frandallfarmer/3DProject/media/thumbnails/log-pillar-walls-2.jpg

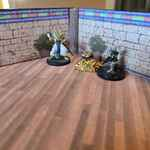
media/thumbnails/log-pillar-walls-2.jpg
