frandallfarmer/3DProject/media/thumbnails/log-wash-agregate-brush.jpg

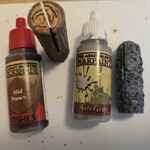
media/thumbnails/log-wash-agregate-brush.jpg
