frandallfarmer/3DProject/wall-templates/1 inch wall template.png

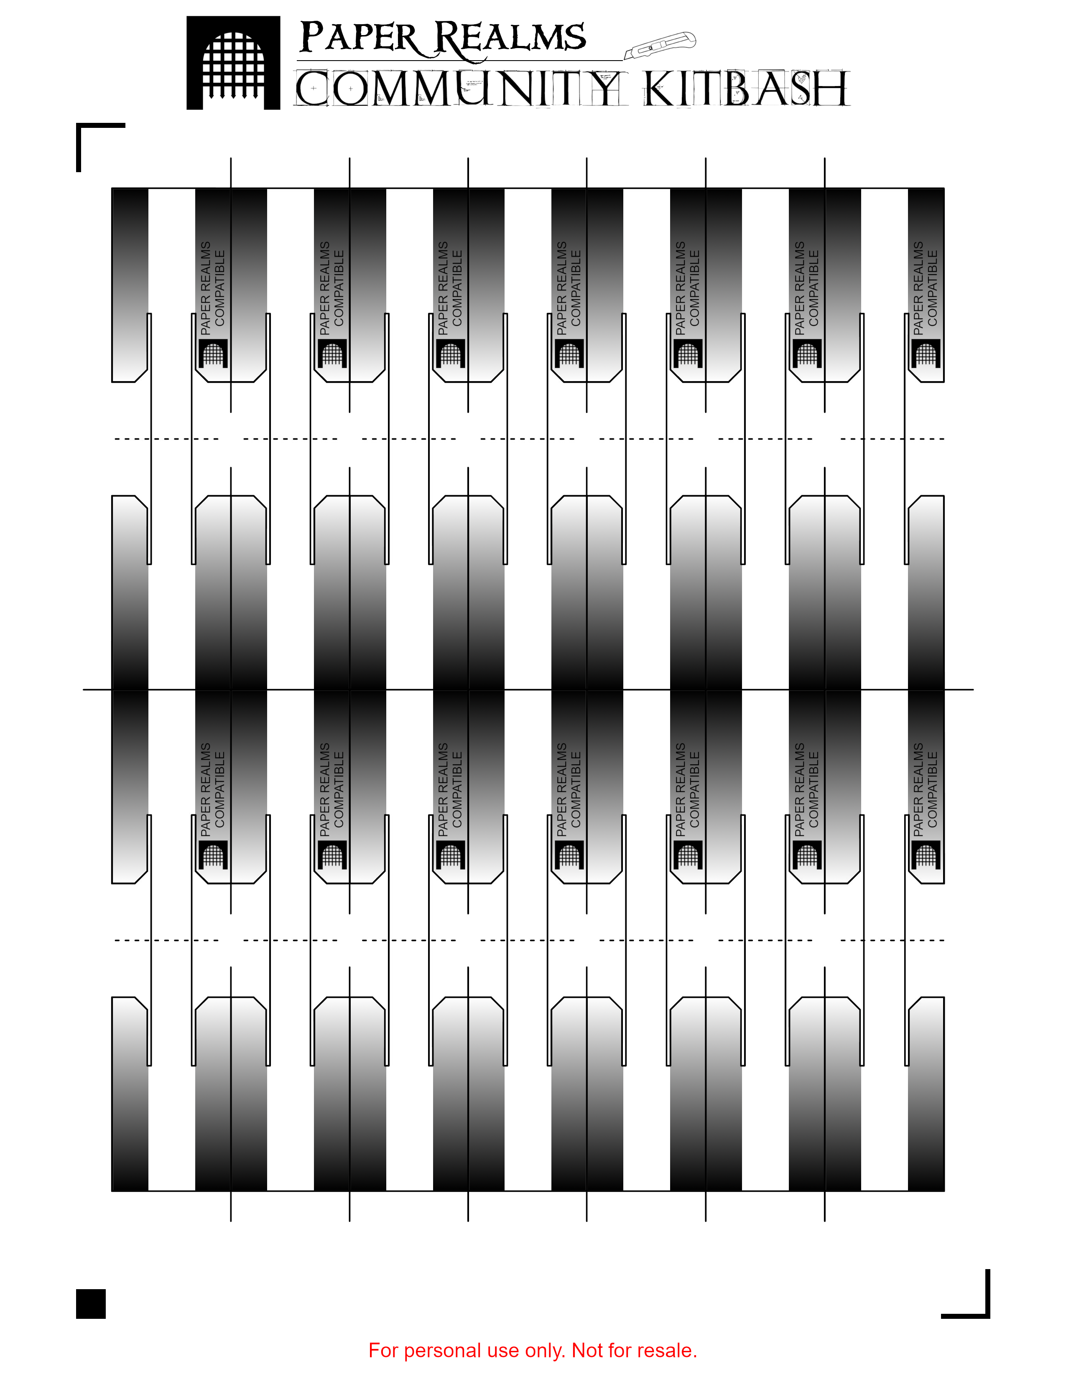
wall-templates/1 inch wall template.png
