frandallfarmer/3DProject/wall-templates/2 inch wall template.png

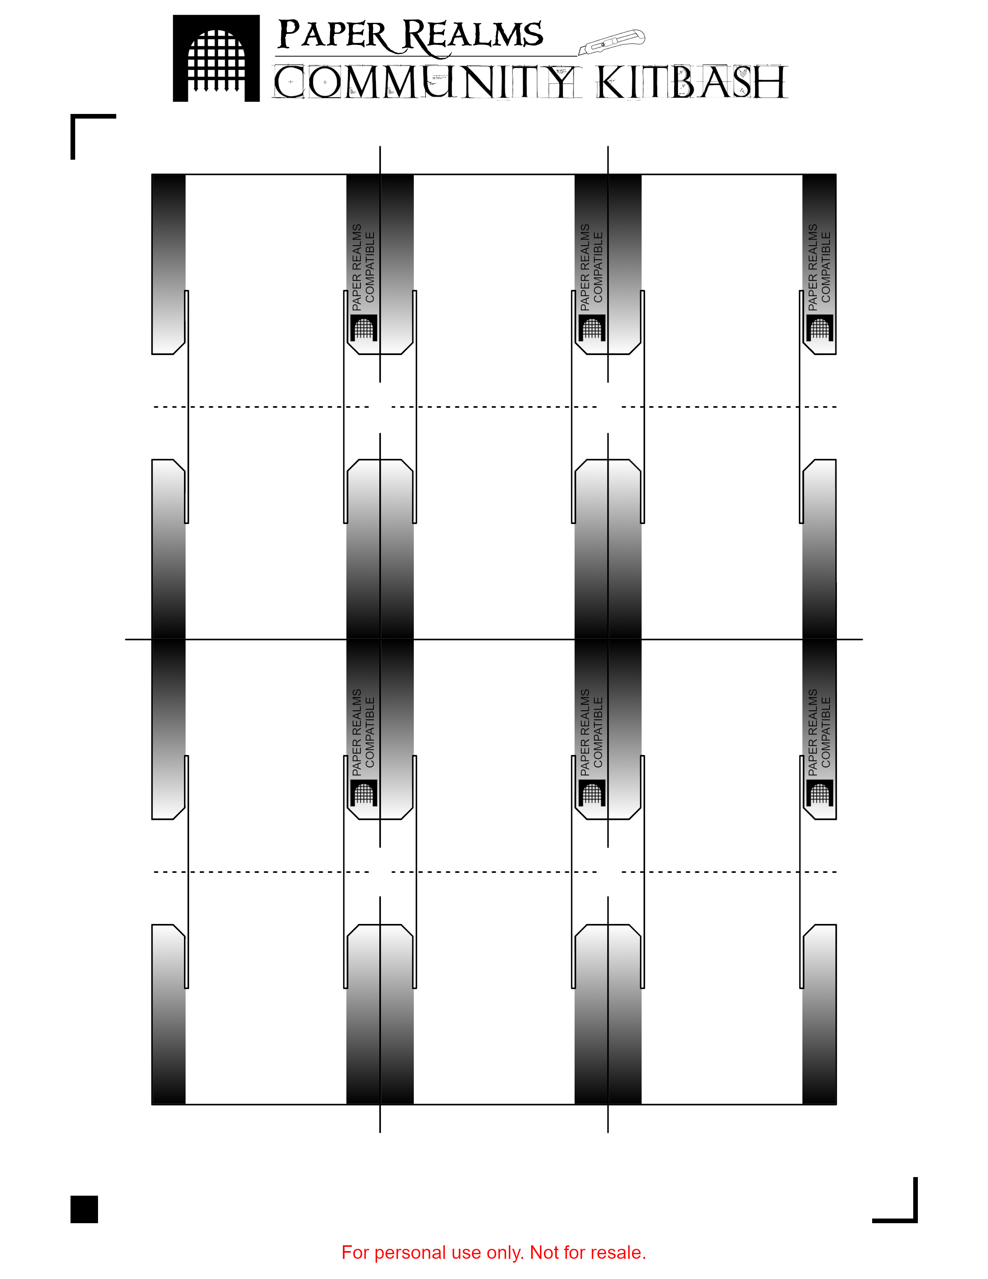
wall-templates/2 inch wall template.png
