frandallfarmer/3DProject/wall-templates/3 inch wall template.png

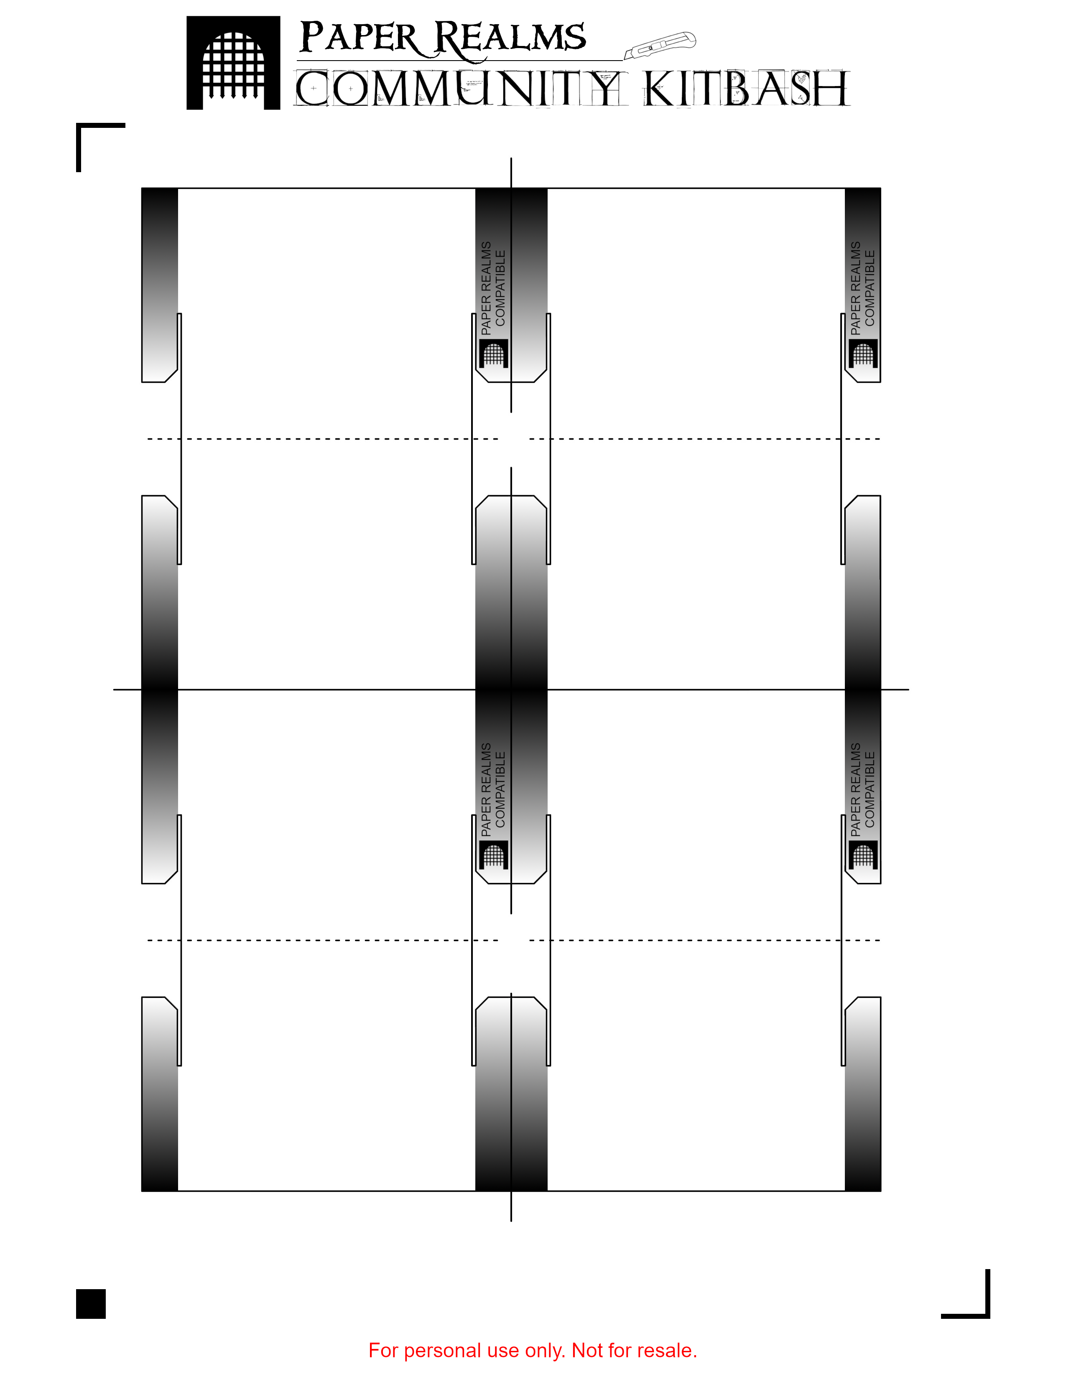
wall-templates/3 inch wall template.png
