frandallfarmer/3DProject/wall-templates/6 inch wall template.png

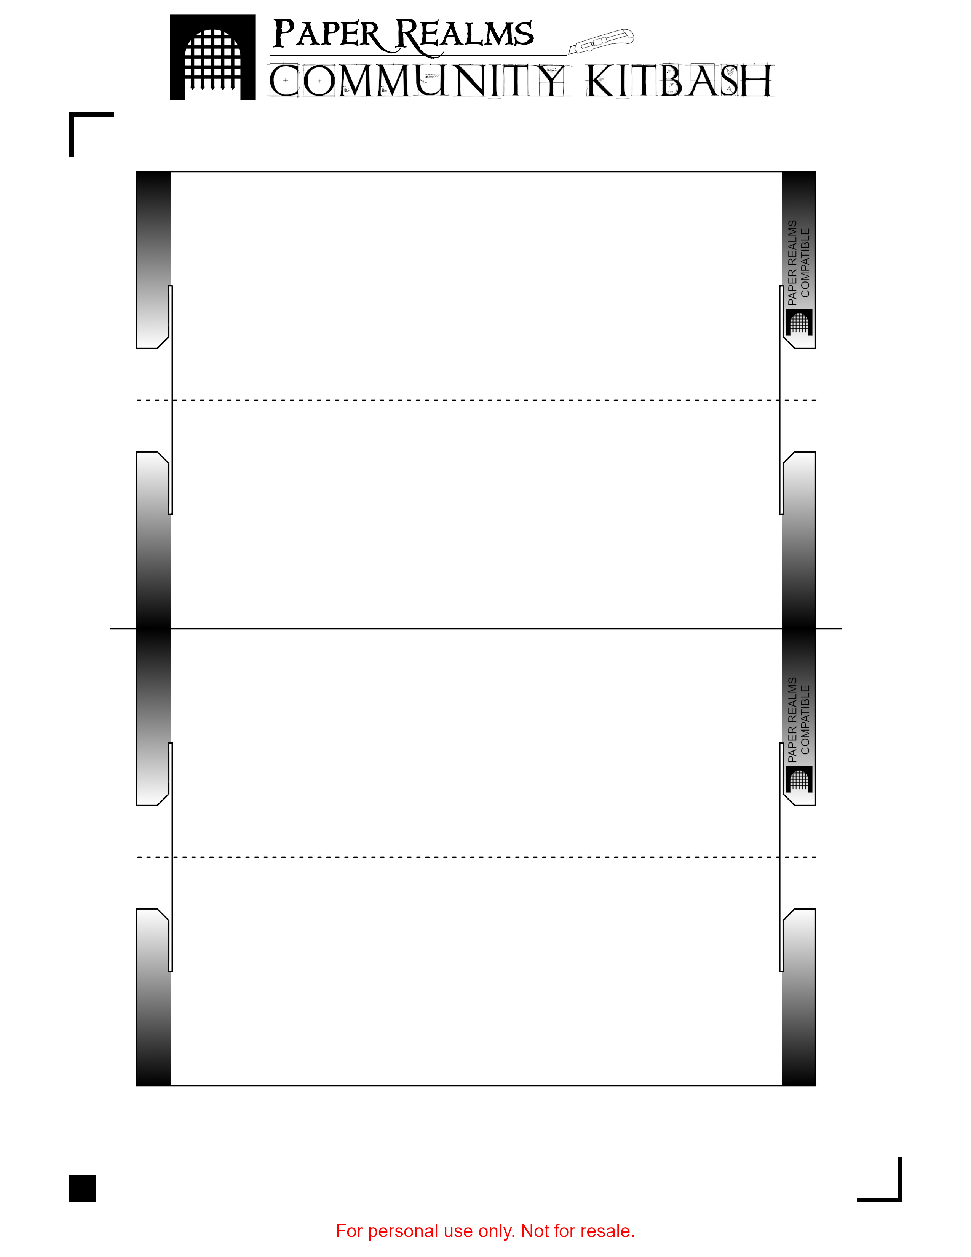
wall-templates/6 inch wall template.png
