frandallfarmer/3DProject/built_stls/output_cobblewall_straight.stl

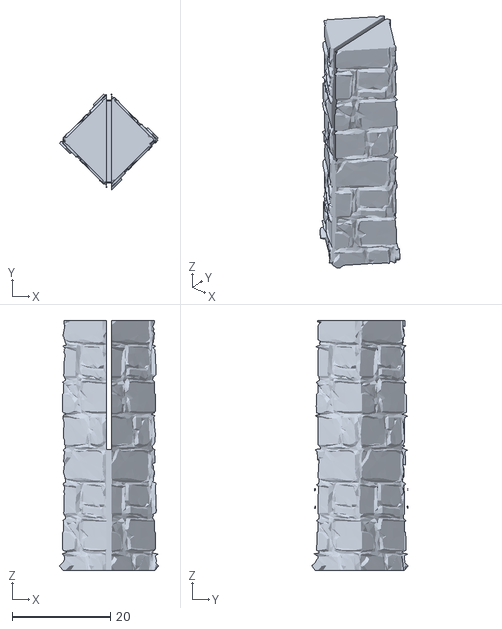
[picture p32: CAD file, 2025-12-31]
built_stls/output_cobblewall_straight.stl
20.1 x 19.5 x 50.8
