frandallfarmer/3DProject/src/pillar_cobblewall.stl

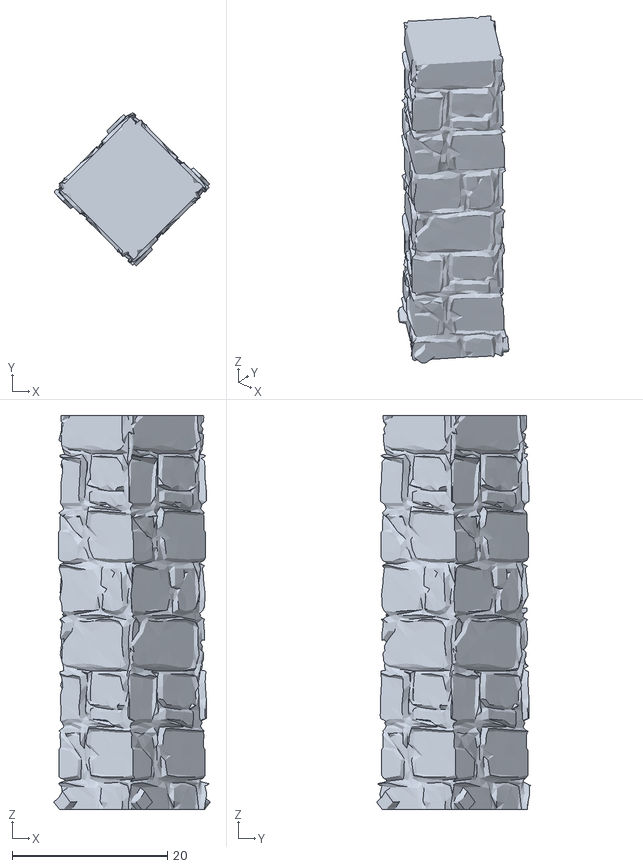
[picture p33: CAD file, 2025-12-16]
src/pillar_cobblewall.stl
20.1 x 19.7 x 50.8
