frandallfarmer/3DProject/src/pillar_cave.stl

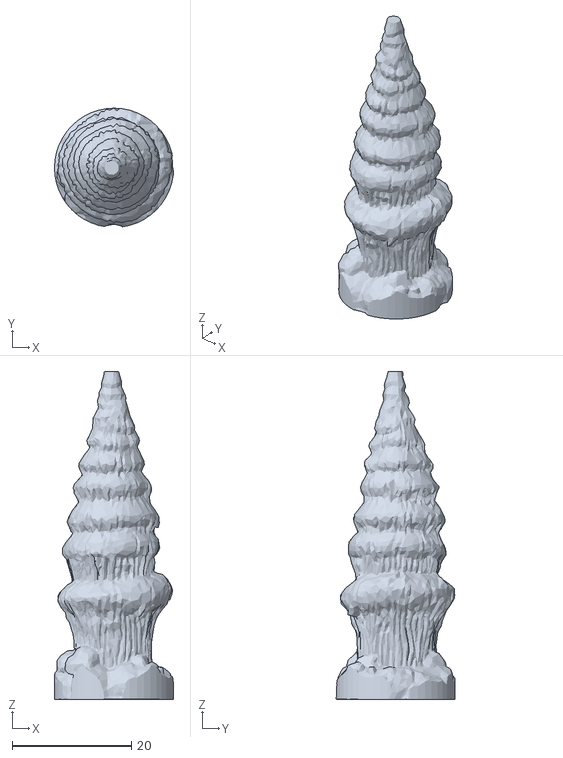
[picture p35: CAD file, 2025-12-16]
src/pillar_cave.stl
20.0 x 19.9 x 55.0
