frandallfarmer/3DProject/built_stls/output_hengestone_tee.stl

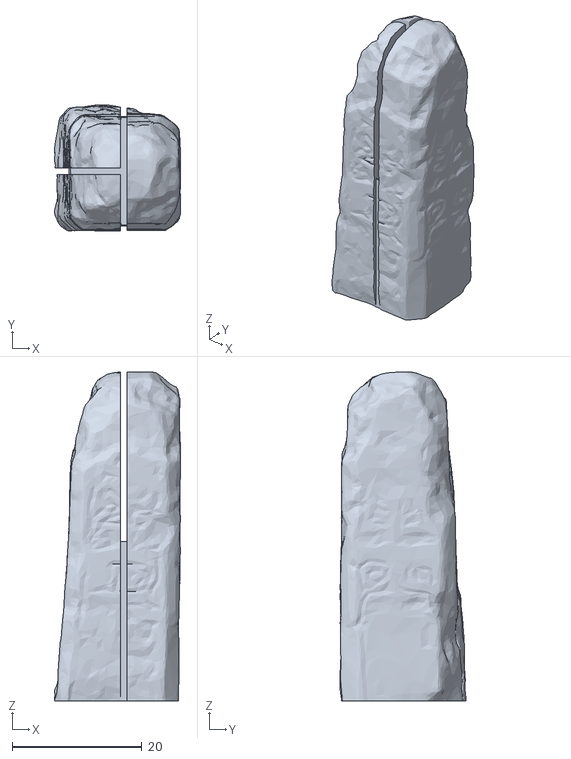
[picture p37: CAD file, 2025-12-31]
built_stls/output_hengestone_tee.stl
19.5 x 19.5 x 50.8
