frandallfarmer/3DProject/built_stls/output_cruciform_allways.stl

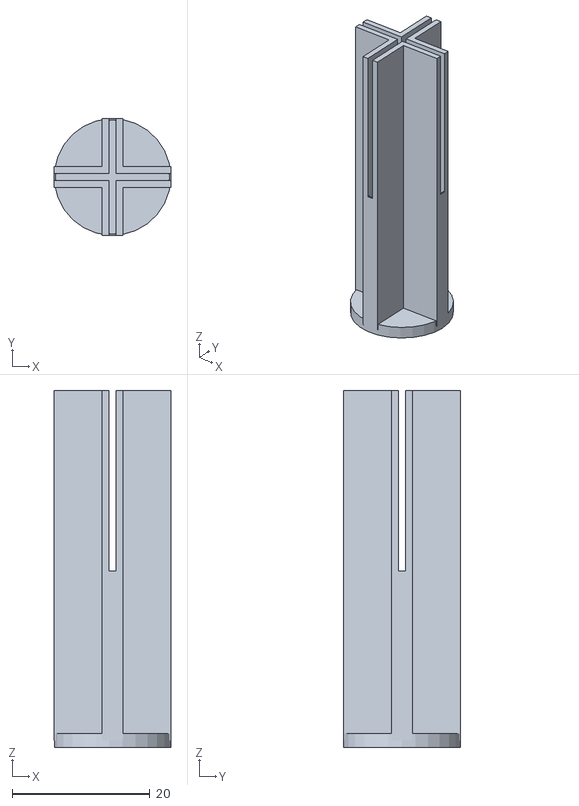
[picture p38: CAD file, 2025-12-31]
built_stls/output_cruciform_allways.stl
16.9 x 16.9 x 51.8
