frandallfarmer/3DProject/built_stls/output_cobblewall_allways.stl

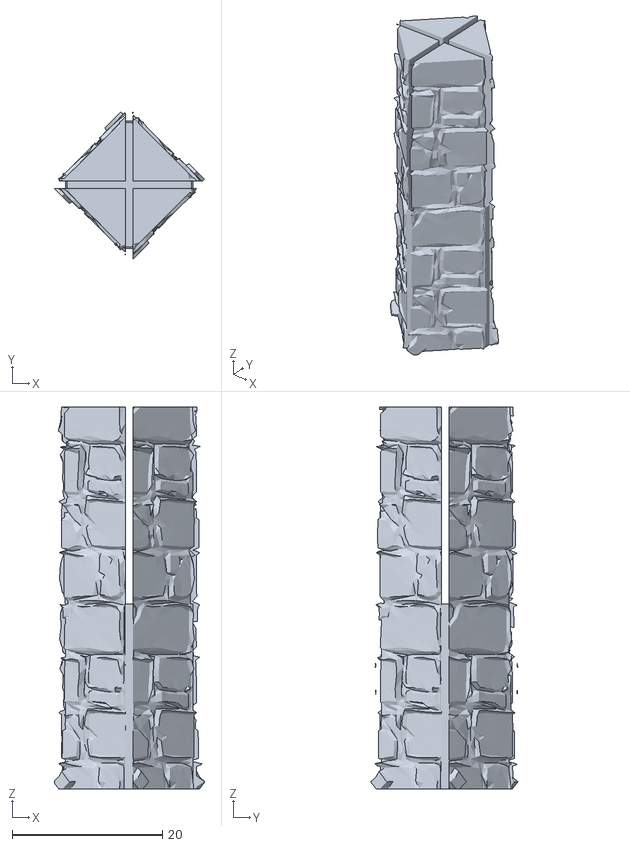
[picture p40: CAD file, 2025-12-31]
built_stls/output_cobblewall_allways.stl
20.0 x 19.5 x 50.8
