frandallfarmer/3DProject/built_stls/output_cruciform_tee.stl

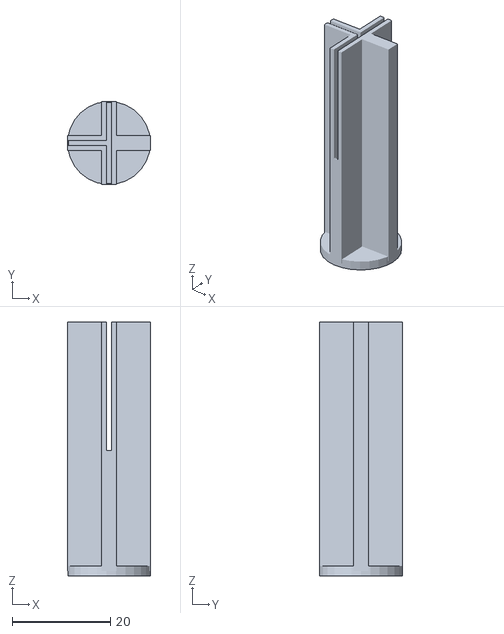
[picture p42: CAD file, 2025-12-31]
built_stls/output_cruciform_tee.stl
16.9 x 16.9 x 51.8
