frandallfarmer/3DProject/built_stls/output_origrect_end.stl

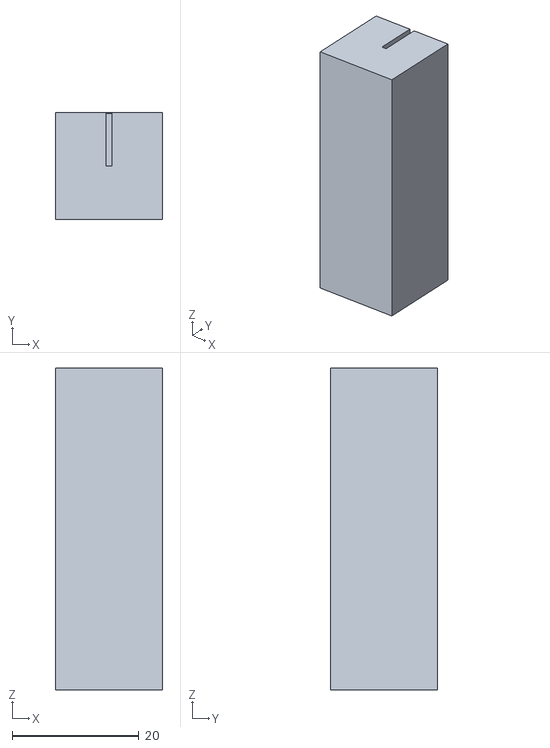
[picture p44: CAD file, 2025-12-31]
built_stls/output_origrect_end.stl
16.9 x 16.9 x 50.8
