frandallfarmer/3DProject/built_stls/output_slimrect_straight.stl

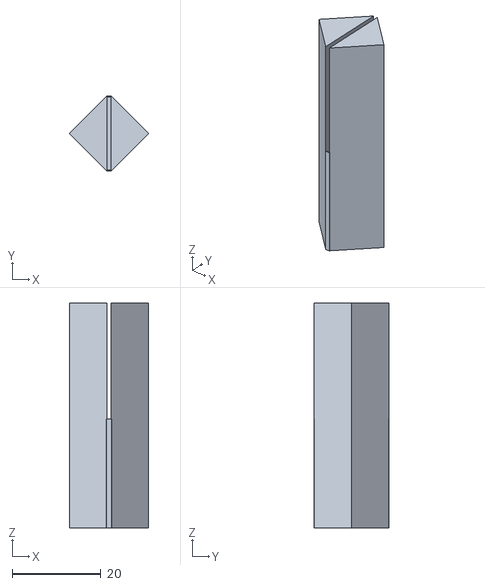
[picture p46: CAD file, 2025-12-31]
built_stls/output_slimrect_straight.stl
17.9 x 16.9 x 50.8
