frandallfarmer/3DProject/built_stls/output_origrect_tee.stl

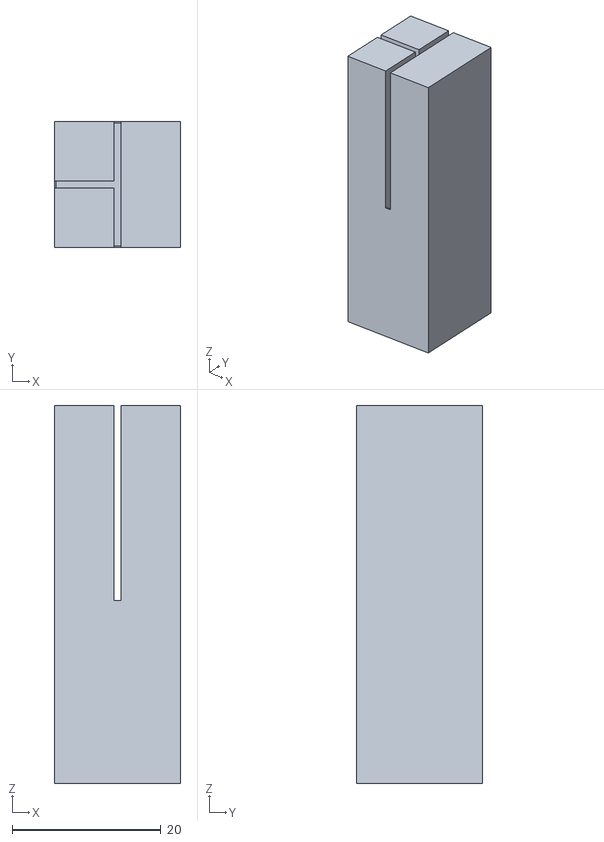
[picture p47: CAD file, 2025-12-31]
built_stls/output_origrect_tee.stl
16.9 x 16.9 x 50.8
