frandallfarmer/3DProject/built_stls/output_woodbeam_tee.stl

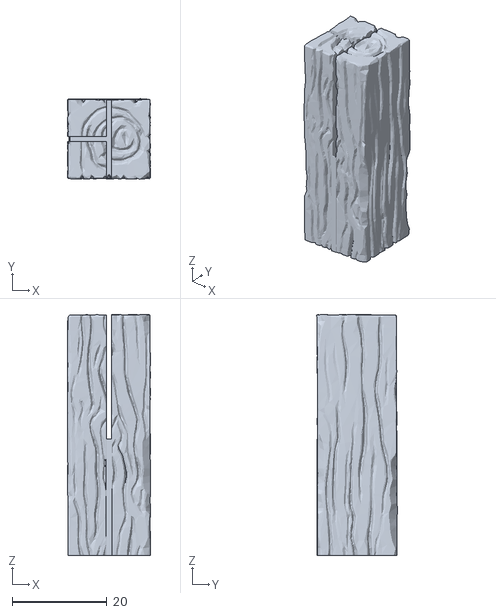
[picture p48: CAD file, 2025-12-31]
built_stls/output_woodbeam_tee.stl
17.5 x 17.0 x 50.8
