frandallfarmer/3DProject/built_stls/output_cobblewall_end.stl

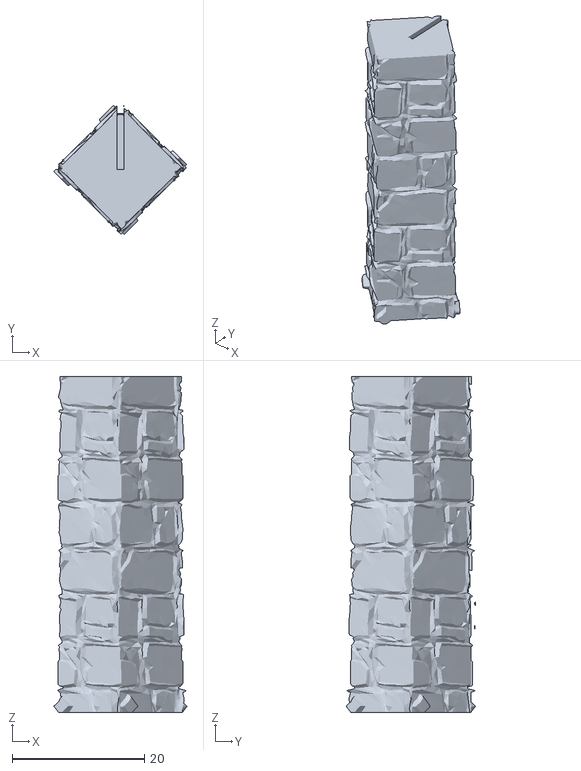
[picture p50: CAD file, 2025-12-31]
built_stls/output_cobblewall_end.stl
20.1 x 19.5 x 50.8
