frandallfarmer/3DProject/built_stls/output_stalagmite_allways.stl

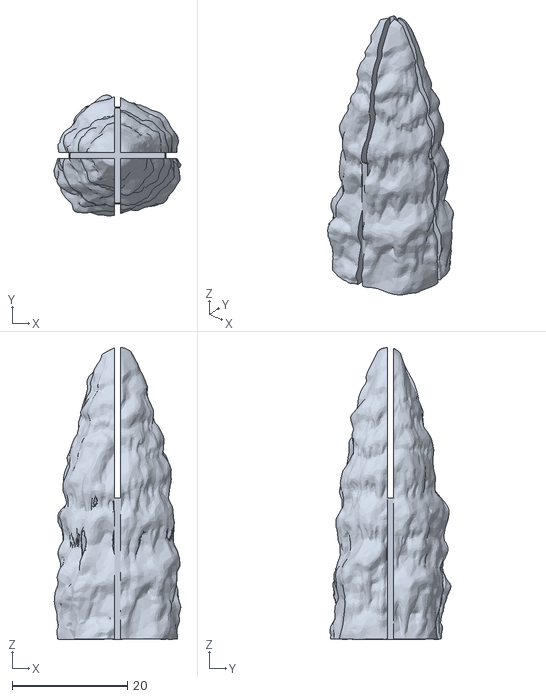
[picture p51: CAD file, 2025-12-31]
built_stls/output_stalagmite_allways.stl
22.0 x 21.0 x 50.7
