frandallfarmer/3DProject/built_stls/output_slimbeam_corner.stl

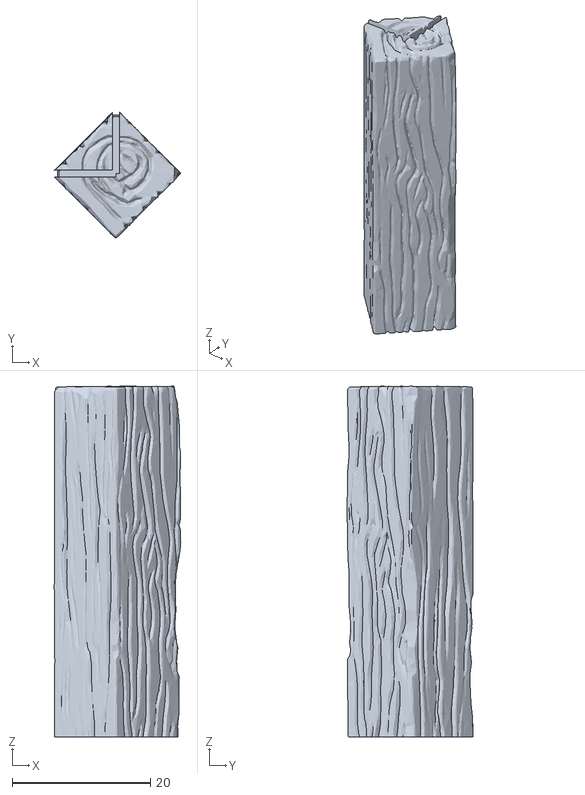
[picture p58: CAD file, 2025-12-31]
built_stls/output_slimbeam_corner.stl
18.3 x 18.2 x 50.8
