frandallfarmer/3DProject/built_stls/output_slimbeam_straight.stl

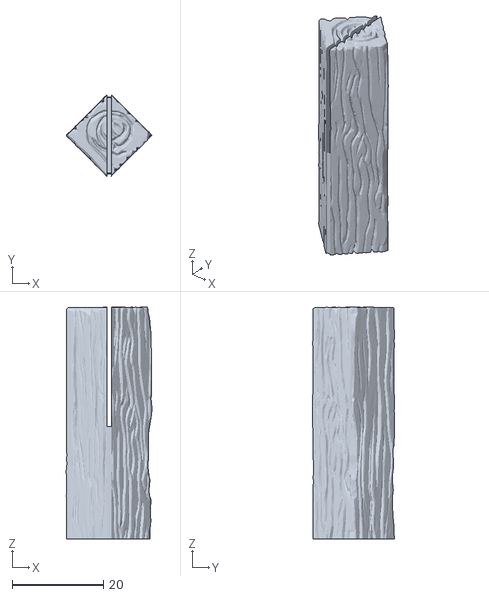
[picture p59: CAD file, 2025-12-31]
built_stls/output_slimbeam_straight.stl
18.8 x 17.9 x 50.8
