frandallfarmer/3DProject/built_stls/output_log_tee.stl

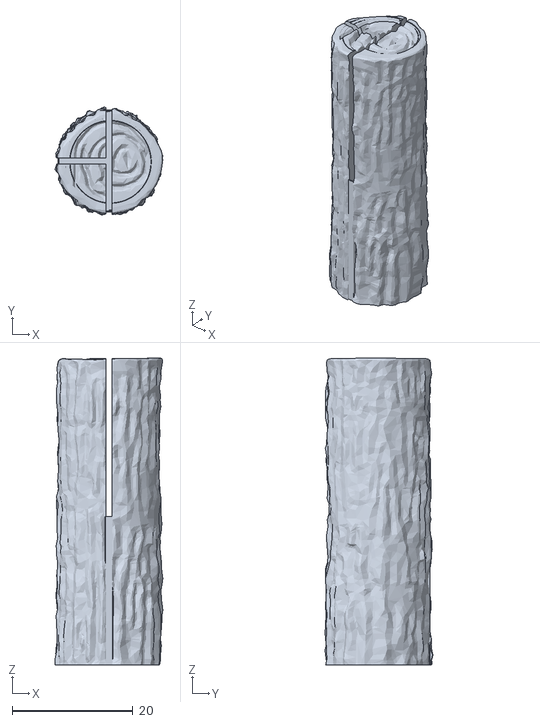
[picture p60: CAD file, 2025-12-31]
built_stls/output_log_tee.stl
17.8 x 17.9 x 50.8
