frandallfarmer/3DProject/built_stls/output_origrect_allways.stl

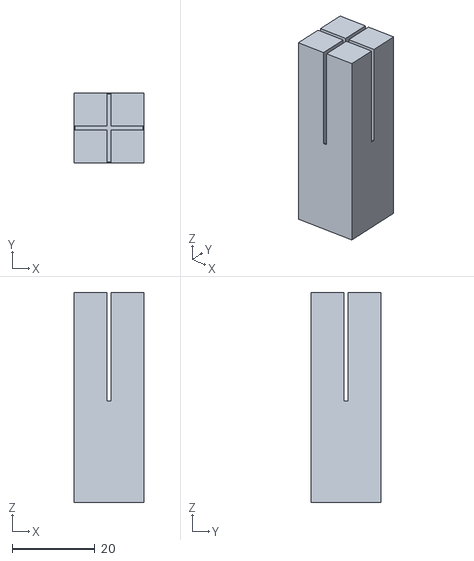
[picture p62: CAD file, 2025-12-31]
built_stls/output_origrect_allways.stl
16.9 x 16.9 x 50.8
