frandallfarmer/3DProject/built_stls/output_stalagmite_end.stl

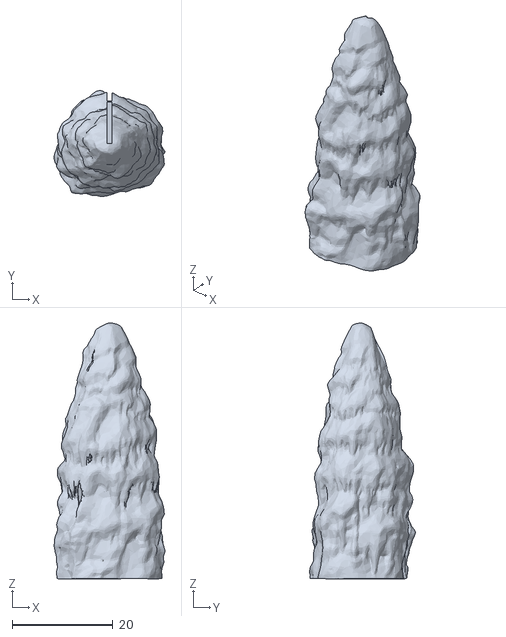
[picture p63: CAD file, 2025-12-31]
built_stls/output_stalagmite_end.stl
22.0 x 21.0 x 50.8
