frandallfarmer/3DProject/built_stls/output_cruciform_end.stl

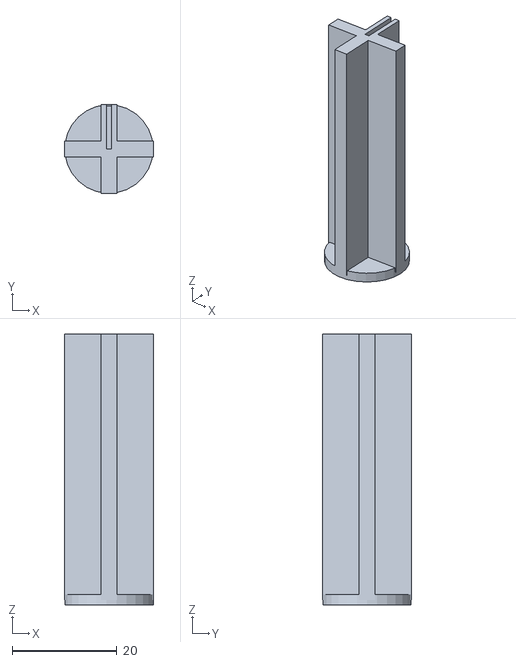
[picture p64: CAD file, 2025-12-31]
built_stls/output_cruciform_end.stl
16.9 x 16.9 x 51.8
