frandallfarmer/3DProject/built_stls/output_slimbeam_tee.stl

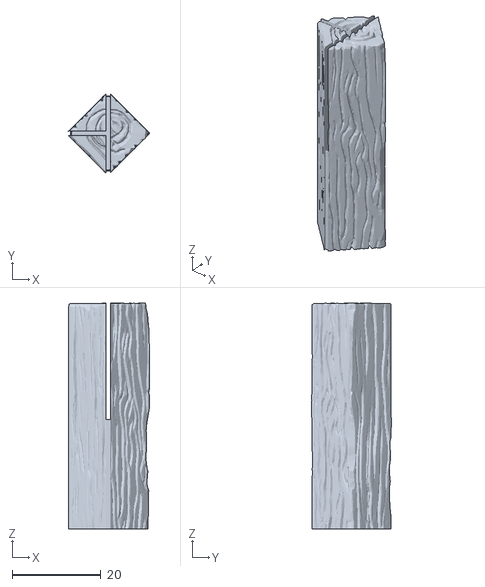
[picture p65: CAD file, 2025-12-31]
built_stls/output_slimbeam_tee.stl
18.3 x 17.9 x 50.8
