frandallfarmer/3DProject/built_stls/output_aggregate_end.stl

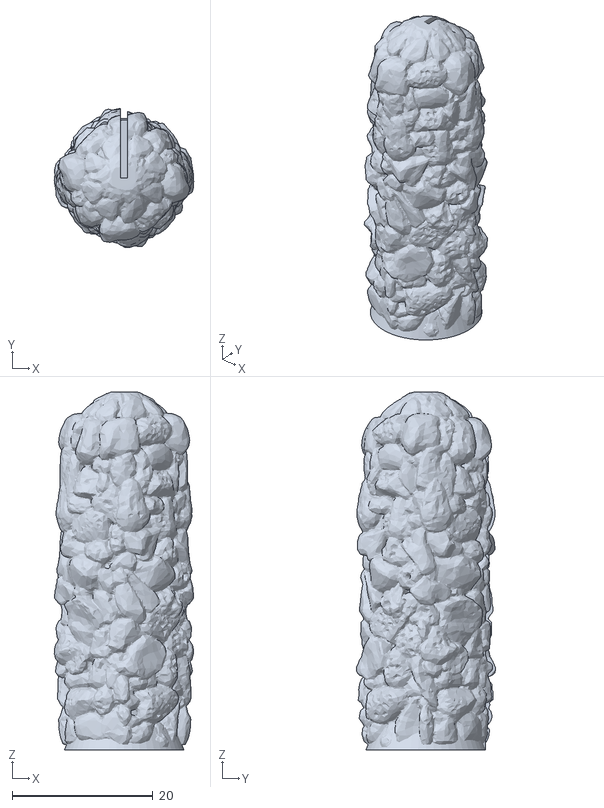
[picture p67: CAD file, 2025-12-31]
built_stls/output_aggregate_end.stl
19.8 x 19.8 x 50.8
