frandallfarmer/3DProject/built_stls/output_slimhengestone_allways.stl

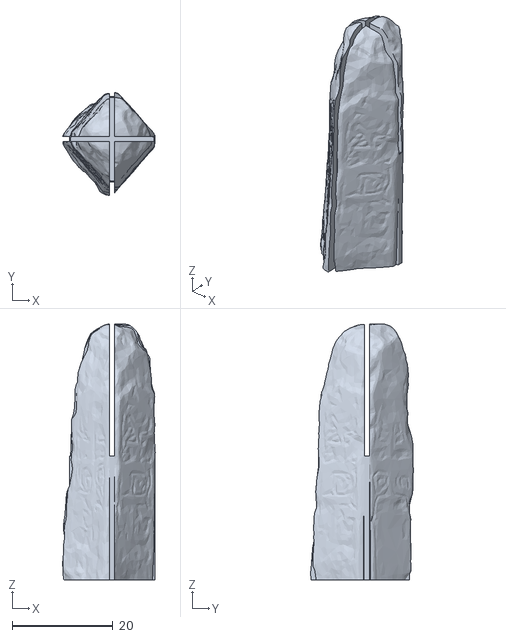
[picture p68: CAD file, 2025-12-31]
built_stls/output_slimhengestone_allways.stl
18.4 x 20.4 x 50.8
