frandallfarmer/3DProject/built_stls/output_woodbeam_allways.stl

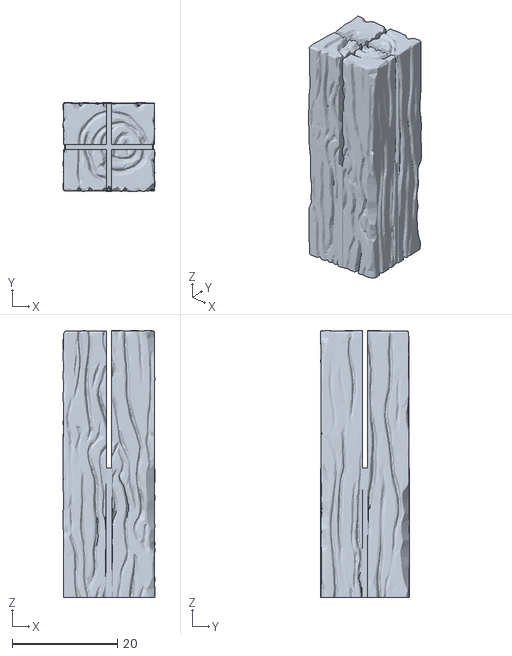
[picture p69: CAD file, 2025-12-31]
built_stls/output_woodbeam_allways.stl
17.5 x 17.0 x 50.8
