frandallfarmer/3DProject/built_stls/output_slimrect_corner.stl

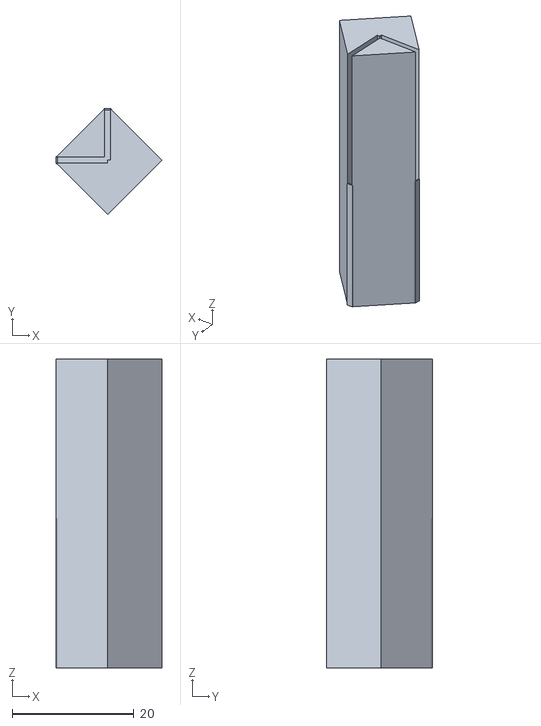
[picture p70: CAD file, 2025-12-31]
built_stls/output_slimrect_corner.stl
17.4 x 17.4 x 50.8
