frandallfarmer/3DProject/built_stls/output_slimbeam_allways.stl

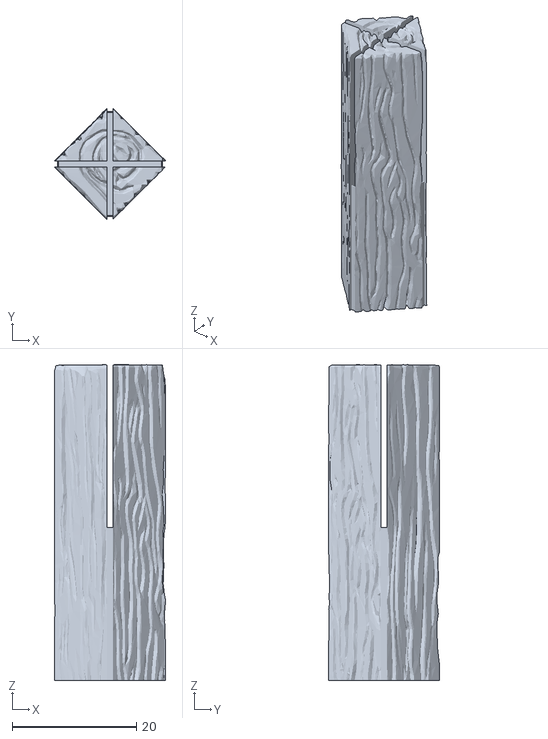
[picture p71: CAD file, 2025-12-31]
built_stls/output_slimbeam_allways.stl
17.9 x 17.9 x 50.8
