frandallfarmer/3DProject/built_stls/output_slimbeam_end.stl

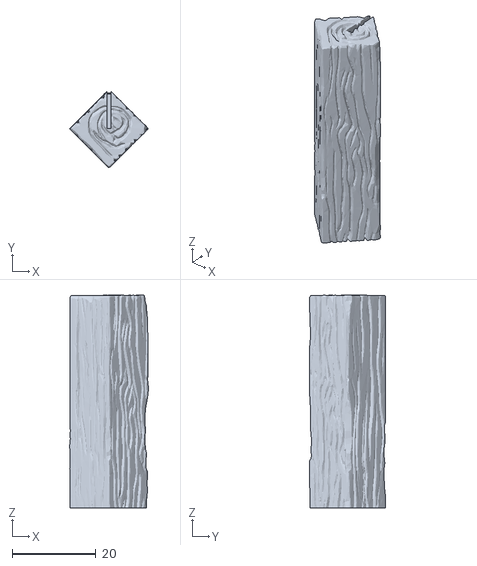
[picture p72: CAD file, 2025-12-31]
built_stls/output_slimbeam_end.stl
18.8 x 18.2 x 50.8
